svofski/lepetomane-control/sw/pio/src/midi.h

#pragma once

#ifdef __cplusplus
extern "C" {
#endif

#include <inttypes.h>

typedef int8_t midi_note_t;
typedef int8_t midi_chan_t;
typedef int8_t midi_prog_t;

typedef void (*midi_note_onoff_cb_t)(midi_chan_t,midi_note_t,uint8_t);
typedef void (*midi_chan_cb_t)(midi_chan_t);
typedef void (*midi_pitchbend_cb_t)(midi_chan_t, int16_t value);
typedef void (*midi_progchange_cb_t)(midi_chan_t, midi_prog_t);
typedef void (*midi_peak_meter_cb_t)(midi_chan_t, uint8_t, uint8_t);

extern midi_note_onoff_cb_t midi_note_on_cb;
extern midi_note_onoff_cb_t midi_note_off_cb;
extern midi_chan_cb_t       midi_all_sound_off_cb;
extern midi_chan_cb_t       midi_all_notes_off_cb;
extern midi_chan_cb_t       midi_reset_all_cntrls_cb;
extern midi_pitchbend_cb_t  midi_pitchbend_cb;
extern midi_progchange_cb_t midi_program_change_cb;
extern midi_peak_meter_cb_t midi_peak_meter_cb;

void midi_read_usbpacket(uint32_t packet32);

void midi_send_cc(uint8_t ctrl, uint8_t value);

#ifdef __cplusplus
}
#endif
