svofski/lepetomane-control/sw/pio/src/usbmidi.c

#include <stdio.h>
#include <libopencm3/usb/usbd.h>
#include "usbcmp_descriptors.h"
#include "usbmidi.h"
#include "midi.h"

/* SysEx identity message, preformatted with correct USB framing information */
const uint8_t sysex_identity[] = {
    0x04,	/* USB Framing (3 byte SysEx) */
    0xf0,	/* SysEx start */
    0x7e,	/* non-realtime */
    0x00,	/* Channel 0 */
    0x04,	/* USB Framing (3 byte SysEx) */
    0x7d,	/* Educational/prototype manufacturer ID */
    0x66,	/* Family code (byte 1) */
    0x66,	/* Family code (byte 2) */
    0x04,	/* USB Framing (3 byte SysEx) */
    0x51,	/* Model number (byte 1) */
    0x19,	/* Model number (byte 2) */
    0x00,	/* Version number (byte 1) */
    0x04,	/* USB Framing (3 byte SysEx) */
    0x00,	/* Version number (byte 2) */
    0x01,	/* Version number (byte 3) */
    0x00,	/* Version number (byte 4) */
    0x05,	/* USB Framing (1 byte SysEx) */
    0xf7,	/* SysEx end */
    0x00,	/* Padding */
    0x00,	/* Padding */
};

static void usbmidi_data_rx_cb(usbd_device *usbd_dev, uint8_t ep)
{
    (void)ep;

    uint32_t buf32[64/4];
    int len = usbd_ep_read_packet(usbd_dev, MIDI_OUT_EP, (uint8_t*)buf32, 64);

    for (int i = 0; i < len/4; ++i) {
        midi_read_usbpacket(buf32[i]);
    }
    
    ///* This implementation treats any message from the host as a SysEx
    // * identity request. This works well enough providing the host
    // * packs the identify request in a single 8 byte USB message.
    // */
    //if (len) {
    //    xprintf("MIDI:");
    //    for (int i = 0; i < len; ++i) {
    //        xprintf("%02x ", buf[i]);
    //    }
    //    xprintf("\n");
    //    //while (usbd_ep_write_packet(usbd_dev, 0x81, sysex_identity,
    //    //            sizeof(sysex_identity)) == 0);
    //}
}

bool midi_config_set = false;

void usbmidi_set_config(usbd_device * usbd_dev, uint16_t value)
{
    (void)value;

    usbd_ep_setup(usbd_dev, MIDI_OUT_EP, USB_ENDPOINT_ATTR_BULK, 64, 
            usbmidi_data_rx_cb);
    usbd_ep_setup(usbd_dev, MIDI_IN_EP, USB_ENDPOINT_ATTR_BULK, 64, NULL);

    midi_config_set = true;
}

void usbmidi_send_cc(usbd_device *usbd_dev, uint8_t ctrl, uint8_t value) {
    char buf[4] = {
        0x0B, /* USB framing: virtual cable 0, note on */
        0xB0, /* MIDI command: control change*/
        ctrl & 0x7F,
        value & 0x7F
    };

    if (!midi_config_set) return;

    while (usbd_ep_write_packet(usbd_dev, MIDI_IN_EP, buf, sizeof(buf)) == 0);
}

void midi_send_cc(uint8_t ctrl, uint8_t value)
{
    extern usbd_device *device;
    if (device) {
        usbmidi_send_cc(device, ctrl, value);
    }
}
