svofski/lepetomane-control/sw/pio/src/Wire/utility/WireBase.h

/******************************************************************************
 * The MIT License
 *
 * Copyright (c) 2010 LeafLabs LLC.
 *
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
 * THE SOFTWARE IS PROVIDED "AS IS", WITHOUT WARRANTY OF ANY KIND,
 * EXPRESS OR IMPLIED, INCLUDING BUT NOT LIMITED TO THE WARRANTIES OF
 * MERCHANTABILITY, FITNESS FOR A PARTICULAR PURPOSE AND
 * NONINFRINGEMENT. IN NO EVENT SHALL THE AUTHORS OR COPYRIGHT HOLDERS
 * BE LIABLE FOR ANY CLAIM, DAMAGES OR OTHER LIABILITY, WHETHER IN AN
 * ACTION OF CONTRACT, TORT OR OTHERWISE, ARISING FROM, OUT OF OR IN
 * CONNECTION WITH THE SOFTWARE OR THE USE OR OTHER DEALINGS IN THE
 * SOFTWARE.
 *****************************************************************************/

/**
 * @file WireBase.h
 * @author Trystan Jones <crenn6977@gmail.com>
 * @brief Wire library, following the majority of the interface from Arduino.
 *        Provides a 'standard' interface to I2C (two-wire) communication for
 *        derived classes.
 */

/*
 * Library created by crenn to allow a system which would provide users the
 * 'standardised' Arduino method for interfacing with I2C devices regardless of
 * whether it is I2C hardware or emulating software.
 */

#ifndef _WIREBASE_H_
#define _WIREBASE_H_

#include "wirish.h"
#include <stdlib.h>
#include <libmaple/i2c.h>

#define BUFFER_LENGTH 32

/* return codes from endTransmission() */
#define SUCCESS   0        /* transmission was successful */
#define EDATA     1        /* too much data */
#define ENACKADDR 2        /* received nack on transmit of address */
#define ENACKTRNS 3        /* received nack on transmit of data */
#define EOTHER    4        /* other error */

class WireBase { // Abstraction is awesome!
protected:
    i2c_msg itc_msg;
    uint8 rx_buf[BUFFER_LENGTH];      /* receive buffer */
    uint8 rx_buf_idx;               /* first unread idx in rx_buf */
    uint8 rx_buf_len;               /* number of bytes read */

    uint8 tx_buf[BUFFER_LENGTH];      /* transmit buffer */
    uint8 tx_buf_idx;  // next idx available in tx_buf, -1 overflow
    bool tx_buf_overflow;

    // Force derived classes to define process function
    virtual uint8 process(uint8) = 0;
    virtual uint8 process() = 0;
public:
    WireBase() {}
    ~WireBase() {}

    /*
     * Initialises the class interface
     */
    // Allow derived classes to overwrite begin function
    virtual void begin(uint8 = 0x00);

    /*
     * Deinitialises the class interface
     */
     // Allow derived classes to overwrite end function
    virtual void end() {}

    /*
     * Sets up the transmission message to be processed
     */
    void beginTransmission(uint8);

    /*
     * Allow only 8 bit addresses to be used
     */
    void beginTransmission(int);

    /*
     * Call the process function to process the message if the TX
     * buffer has not overflowed.
     */
    uint8 endTransmission(bool);
    uint8 endTransmission(void);

    /*
     * Request bytes from a slave device and process the request,
     * storing into the receiving buffer.
     */
    uint8 requestFrom(uint8, int,bool stop=false);

    /*
     * Allow only 8 bit addresses to be used when requesting bytes
     */
    uint8 requestFrom(int address, int numBytes, bool stop=true);
	

    /*
     * Stack up bytes to be sent when transmitting
     */
    size_t write(uint8);

    /*
     * Stack up bytes from the array to be sent when transmitting
     */
    size_t write(uint8*, int);
    size_t write(const uint8* buf, int nr) { write((uint8*)buf,nr); }

    /*
     * Ensure that a sending data will only be 8-bit bytes
     */
    size_t write(int);

    /*
     * Ensure that an array sending data will only be 8-bit bytes
     */
    size_t write(int*, int);

    /*
     * Stack up bytes from a string to be sent when transmitting
     */
    void write(char*);

    /*
     * Return the amount of bytes that is currently in the receiving buffer
     */
    uint8 available();

    /*
     * Return the value of byte in the receiving buffer that is currently being
     * pointed to
     */
    uint8 read();
};

#endif // _WIREBASE_H_
